hide63414/FV-1_Reverb_Effects_Developer_Kit/img/BOX/BoxHoleDrilling2.jpg

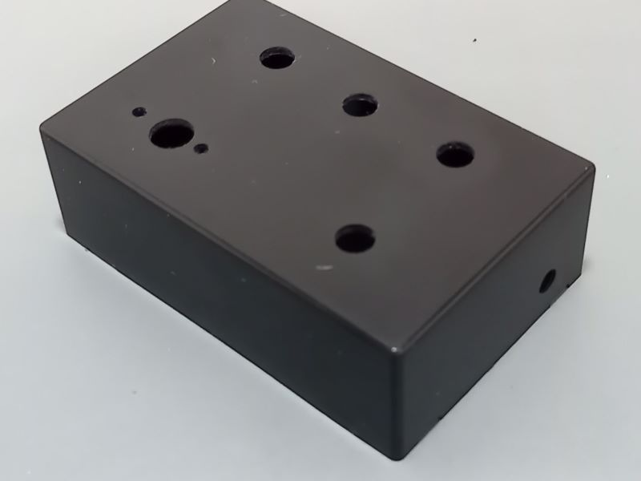
img/BOX/BoxHoleDrilling2.jpg
