hide63414/FV-1_Reverb_Effects_Developer_Kit/img/BOX/RotarySwitch_panelize.jpg

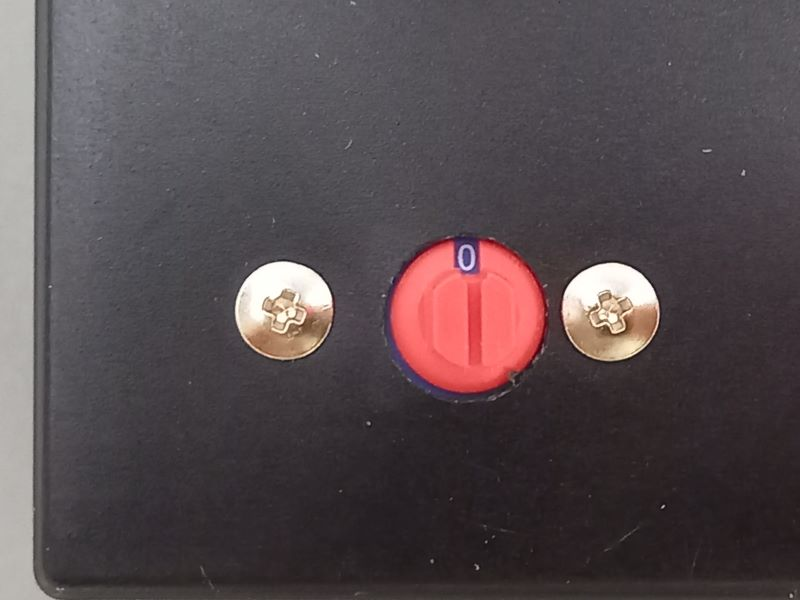
img/BOX/RotarySwitch_panelize.jpg
