hide63414/FV-1_Reverb_Effects_Developer_Kit/img/EEPROM/HexToBin.jpg

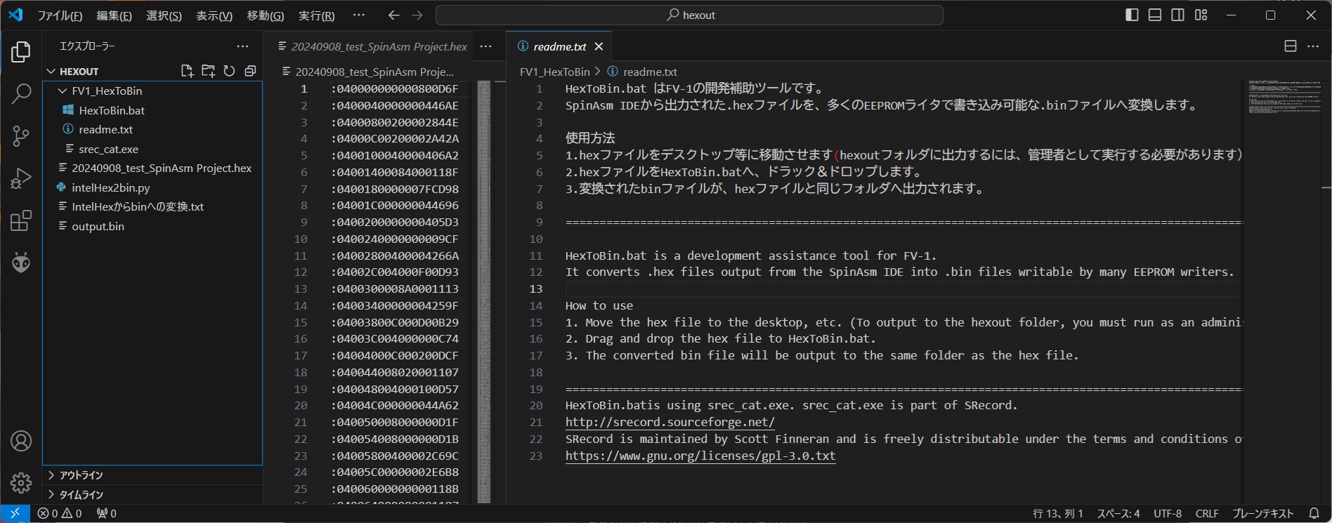
img/EEPROM/HexToBin.jpg
